jcksnvllxr80/MidiControllerCpp/src/adapters/mcu/WifiManager.cpp

#include "mc/adapters/mcu/WifiManager.h"

#include <algorithm>

#include "mc/adapters/mcu/Log.h"

#include "pico/cyw43_arch.h"
#include "pico/time.h"  // to_ms_since_boot / get_absolute_time

#include "lwip/apps/mdns.h"
#include "lwip/ip4_addr.h"
#include "lwip/netif.h"
#include "lwip/pbuf.h"
#include "lwip/tcp.h"

#include <nlohmann/json.hpp>

#include "mc/app/EditorProtocol.h"

namespace mc::mcu {

namespace {
using json = nlohmann::json;

constexpr uint32_t kConnectTimeoutMs = 15000;  // give up one async join attempt after this
constexpr uint32_t kRetryIntervalMs = 5000;    // wait before re-trying after a failure / drop
uint32_t nowMs() { return to_ms_since_boot(get_absolute_time()); }

err_t tcpRecvTramp(void* arg, tcp_pcb* pcb, pbuf* p, err_t err) {
    auto* self = static_cast<WifiManager*>(arg);
    if (p == nullptr) {
        self->onRecv(pcb, nullptr, 0, true);
        return ERR_OK;
    }
    if (err == ERR_OK) {
        for (pbuf* q = p; q; q = q->next) self->onRecv(pcb, q->payload, q->len, false);
        tcp_recved(pcb, p->tot_len);
    }
    pbuf_free(p);
    return ERR_OK;
}
err_t tcpSentTramp(void* arg, tcp_pcb*, u16_t) {
    static_cast<WifiManager*>(arg)->onSent();
    return ERR_OK;
}
void tcpErrTramp(void* arg, err_t) { static_cast<WifiManager*>(arg)->onClientErr(); }
err_t tcpAcceptTramp(void* arg, tcp_pcb* newpcb, err_t err) {
    if (err != ERR_OK || newpcb == nullptr) return ERR_VAL;
    static_cast<WifiManager*>(arg)->onAccept(newpcb);
    return ERR_OK;
}
void mdnsSrvTxt(struct mdns_service* service, void* /*txt_userdata*/) {
    mdns_resp_add_service_txtitem(service, "version=1", 9);
}
}  // namespace

WifiManager::WifiManager(IConfigStore& store, uint16_t tcpPort) : store_(store), port_(tcpPort) {}

void WifiManager::emitStatus(const std::string& msg) {
    if (statusSink_) statusSink_(msg);
}

void WifiManager::loadConfig() {
    if (!store_.exists("wifi.json")) return;
    try {
        auto j = json::parse(store_.read("wifi.json"));
        ssid_ = j.value("ssid", std::string());
        password_ = j.value("password", std::string());
        enabled_ = j.value("enabled", false);
    } catch (...) {
        // corrupt config -> ignore, stay off
    }
}

void WifiManager::saveConfig() {
    json j;
    j["ssid"] = ssid_;
    j["password"] = password_;
    j["enabled"] = enabled_;
    store_.write("wifi.json", j.dump());
}

void WifiManager::begin() {
    loadConfig();
    LOG_I("wifi", "begin enabled=%d ssid='%s'", (int)enabled_, ssid_.c_str());
    if (cyw43_arch_init()) {
        LOG_E("wifi", "cyw43 init failed");
        emitStatus("WiFi: init failed");
        return;
    }
    inited_ = true;
    cyw43_arch_enable_sta_mode();
    if (enabled_ && !ssid_.empty()) startConnect();  // non-blocking; poll() drives it
}

void WifiManager::poll() {
    if (!inited_) return;
    cyw43_arch_poll();
    serviceLink();
}

// Kick off a non-blocking join. The outcome is observed in serviceLink() via the
// link status, so this returns immediately and never stalls the main loop.
void WifiManager::startConnect() {
    if (!inited_ || !enabled_ || ssid_.empty()) return;
    uint32_t auth = password_.empty() ? CYW43_AUTH_OPEN : CYW43_AUTH_WPA2_AES_PSK;
    lastAttemptMs_ = nowMs();
    LOG_I("wifi", "connecting to '%s'", ssid_.c_str());
    if (cyw43_arch_wifi_connect_async(ssid_.c_str(), password_.c_str(), auth) != 0) {
        link_ = Link::Idle;  // couldn't even start -> serviceLink() retries after backoff
        LOG_E("wifi", "connect async start failed");
        emitStatus("WiFi: connect failed");
        return;
    }
    link_ = Link::Connecting;
    connectStartMs_ = lastAttemptMs_;
    emitStatus("WiFi: connecting");
}

// The point of this rewrite: a non-blocking state machine that finishes the boot
// join without stalling, reconnects automatically if the link drops, and never
// blocks long enough to trip the watchdog.
void WifiManager::serviceLink() {
    if (!enabled_ || ssid_.empty()) return;  // nothing to maintain
    int st = cyw43_tcpip_link_status(&cyw43_state, CYW43_ITF_STA);
    switch (link_) {
        case Link::Connecting:
            if (st == CYW43_LINK_UP) {
                onLinkUp();
            } else if (st < 0 || (nowMs() - connectStartMs_) > kConnectTimeoutMs) {
                connected_ = false;  // failed (bad auth / no net) or timed out
                ip_.clear();
                link_ = Link::Idle;
                lastAttemptMs_ = nowMs();
                LOG_W("wifi", "connect failed/timeout (st=%d) retrying in %lus", st, (unsigned long)(kRetryIntervalMs/1000));
                emitStatus("WiFi: retrying");
            }
            break;
        case Link::Up:
            if (st != CYW43_LINK_UP) {  // dropped under us
                connected_ = false;
                ip_.clear();
                teardownNet();
                link_ = Link::Idle;
                lastAttemptMs_ = nowMs();
                LOG_W("wifi", "link lost (st=%d)", st);
                emitStatus("WiFi: link lost");
            }
            break;
        case Link::Idle:
            if (nowMs() - lastAttemptMs_ >= kRetryIntervalMs) startConnect();
            break;
    }
}

void WifiManager::onLinkUp() {
    link_ = Link::Up;
    connected_ = true;
    ip_ = ip4addr_ntoa(netif_ip4_addr(netif_default));
    startServer();  // rebinds if a previous drop tore it down
    startMdns();
    LOG_I("wifi", "connected ssid='%s' ip=%s port=%u", ssid_.c_str(), ip_.c_str(), port_);
    emitStatus("WiFi " + ip_);
}

void WifiManager::teardownNet() {
    if (client_) {
        tcp_arg(client_, nullptr);
        tcp_close(client_);
        client_ = nullptr;
    }
    if (listen_) {
        tcp_close(listen_);
        listen_ = nullptr;
    }
    rxLine_.clear();
    outbox_.clear();
    outSent_ = 0;
}

void WifiManager::disconnectNow() {
    LOG_I("wifi", "disconnecting");
    teardownNet();
    if (inited_) cyw43_wifi_leave(&cyw43_state, CYW43_ITF_STA);
    link_ = Link::Idle;
    connected_ = false;
    ip_.clear();
    emitStatus("WiFi: off");
}

void WifiManager::startServer() {
    if (listen_) return;
    tcp_pcb* p = tcp_new_ip_type(IPADDR_TYPE_ANY);
    if (!p) return;
    if (tcp_bind(p, IP_ANY_TYPE, port_) != ERR_OK) {
        tcp_close(p);
        return;
    }
    listen_ = tcp_listen_with_backlog(p, 1);
    if (!listen_) {
        tcp_close(p);
        return;
    }
    tcp_arg(listen_, this);
    tcp_accept(listen_, tcpAcceptTramp);
}

void WifiManager::startMdns() {
    if (mdnsUp_) return;
    mdns_resp_init();
    mdns_resp_add_netif(netif_default, "midicontroller");
    mdns_resp_add_service(netif_default, "MidiController", "_midicontroller", DNSSD_PROTO_TCP, port_, mdnsSrvTxt,
                          nullptr);
    mdnsUp_ = true;
}

void WifiManager::onAccept(tcp_pcb* newpcb) {
    LOG_I("wifi", "TCP client connected (replacing=%d)", client_ != nullptr);
    if (client_) {  // single client: replace the old one
        tcp_arg(client_, nullptr);
        tcp_close(client_);
    }
    client_ = newpcb;
    rxLine_.clear();
    outbox_.clear();
    outSent_ = 0;
    tcp_arg(client_, this);
    tcp_recv(client_, tcpRecvTramp);
    tcp_sent(client_, tcpSentTramp);
    tcp_err(client_, tcpErrTramp);
}

void WifiManager::onRecv(tcp_pcb* pcb, const void* data, uint16_t len, bool closed) {
    if (closed) {
        if (client_ == pcb) {
            LOG_I("wifi", "TCP client disconnected");
            tcp_arg(pcb, nullptr);
            tcp_close(pcb);
            client_ = nullptr;
            rxLine_.clear();
            outbox_.clear();
            outSent_ = 0;
        }
        return;
    }
    const char* p = static_cast<const char*>(data);
    for (uint16_t i = 0; i < len; ++i) {
        char c = p[i];
        if (c == '\n') {
            LOG_D("wifi", "cmd (%zu): %.120s%s", rxLine_.size(), rxLine_.c_str(),
                  rxLine_.size() > 120 ? "..." : "");
            if (proto_) outbox_ += proto_->handleLine(rxLine_);
            rxLine_.clear();
        } else if (c != '\r' && rxLine_.size() < 128 * 1024) {
            rxLine_.push_back(c);
        }
    }
    trySend();
}

void WifiManager::trySend() {
    if (!client_) return;
    while (outSent_ < outbox_.size()) {
        u16_t avail = tcp_sndbuf(client_);
        if (avail == 0) break;
        u16_t n = static_cast<u16_t>(std::min<size_t>(avail, outbox_.size() - outSent_));
        if (tcp_write(client_, outbox_.data() + outSent_, n, TCP_WRITE_FLAG_COPY) != ERR_OK) break;
        outSent_ += n;
    }
    tcp_output(client_);
    if (outSent_ >= outbox_.size()) {
        outbox_.clear();
        outSent_ = 0;
    }
}

void WifiManager::onSent() { trySend(); }

void WifiManager::onClientErr() {
    LOG_W("wifi", "TCP client error — connection dropped");
    client_ = nullptr;  // lwIP already freed the pcb
    rxLine_.clear();
    outbox_.clear();
    outSent_ = 0;
}

void WifiManager::setCredentials(const std::string& ssid, const std::string& password) {
    ssid_ = ssid;
    password_ = password;
    enabled_ = true;  // setting credentials implies "use this network"
    saveConfig();
    if (inited_) {
        disconnectNow();  // leave any old network + tear down
        startConnect();   // non-blocking join to the new one
    }
}

void WifiManager::setEnabled(bool on) {
    enabled_ = on;
    saveConfig();
    if (!inited_) return;
    if (on) {
        if (link_ == Link::Idle) startConnect();  // no-op if already connecting/up
    } else {
        disconnectNow();
    }
}

WifiStatus WifiManager::status() const {
    WifiStatus s;
    s.enabled = enabled_;
    s.connected = connected_;
    s.ssid = ssid_;
    s.ip = ip_;
    return s;
}

}  // namespace mc::mcu
