jcksnvllxr80/MidiControllerCpp/include/mc/app/Application.h

#pragma once
//
// Application — the composition root and event loop. Ports the setup()/main()
// glue from midi_controller.py plus the song/set/part navigation from
// RotaryEncoder.py:
//   * builds MidiPedals from the channel table (in channel order)
//   * footswitches preview (displayed) song/part; "Select" commits (loads MIDI)
//   * long-press footswitches commit immediately (change_and_select)
//   * the rotary knob drives the MenuTree (setup/global/power)
//
// All hardware is behind ports, so the same Application runs on the sim now and
// the microcontroller later.
//
#include <algorithm>
#include <functional>
#include <map>
#include <memory>
#include <string>
#include <vector>

#include "mc/domain/ControllerState.h"
#include "mc/domain/MenuTree.h"
#include "mc/domain/MidiPedal.h"
#include "mc/domain/PedalConfig.h"
#include "mc/domain/SongPartSet.h"
#include "mc/ports/IClock.h"
#include "mc/ports/IConfigStore.h"
#include "mc/ports/IConfigTransport.h"
#include "mc/ports/IDisplay.h"
#include "mc/ports/IInput.h"
#include "mc/ports/ILed.h"
#include "mc/ports/IMidiOut.h"

namespace mc {

class Application {
public:
    struct Ports {
        IConfigStore* store = nullptr;
        IMidiOut* midi = nullptr;
        IDisplay* display = nullptr;
        ILed* led = nullptr;
        IClock* clock = nullptr;
        IInput* input = nullptr;
        IConfigTransport* transport = nullptr;  // optional
    };

    explicit Application(Ports ports);

    void setup();        // load config, build pedals/menu, set initial display
    void run();          // poll input -> dispatch until Quit / source exhausted
    bool handleEvent(const InputEvent& ev);  // false => stop loop
    void tick();         // periodic housekeeping (debounced "save defaults"); call each loop iter

    // Optional: invoked once per handled input/command (physical or editor) so a
    // host can flash an activity indicator. Portable code stays hardware-agnostic.
    void setActivitySink(std::function<void()> fn) { activitySink_ = std::move(fn); }

    bool setupFailed() const { return setupFailed_; }  // config parse fell back to a safe shell

    // --- inspectors (for tests) ---
    ControllerState& state() { return state_; }
    Setlist& setlist() { return setlist_; }
    MenuTree& menu() { return menu_; }
    const std::string& currentSongName() const { return currentSong().name; }
    const std::string& currentPartName() const { return currentPart().name; }
    const std::string& displayedSongName() const { return displayedSong().name; }
    const std::string& displayedPartName() const { return displayedPart().name; }
    const std::string& displayedMessage() const { return lastMessage_; }  // last text shown
    bool quitRequested() const { return quitRequested_; }

    // Navigation, exposed so tests/menus can drive them directly.
    void loadPart();
    void loadSong();
    void selectChoice();
    void nextSong();
    void prevSong();
    void nextPart();
    void prevPart();

private:
    // Bounds-safe so a corrupt/empty config (see setup()'s fallback) degrades to a
    // blank song/part instead of throwing out_of_range and taking the device down.
    const Song& songAt(int i) const {
        static const Song kEmpty;
        if (setlist_.songs.empty()) return kEmpty;
        return setlist_.songs[std::min(std::max(i, 0), static_cast<int>(setlist_.songs.size()) - 1)];
    }
    static const Part& partAt(const Song& s, int i) {
        static const Part kEmpty;
        if (s.parts.empty()) return kEmpty;
        return s.parts[std::min(std::max(i, 0), static_cast<int>(s.parts.size()) - 1)];
    }
    const Song& currentSong() const { return songAt(currentSongIdx_); }
    const Part& currentPart() const { return partAt(currentSong(), currentPartIdx_); }
    const Song& displayedSong() const { return songAt(displayedSongIdx_); }
    const Part& displayedPart() const { return partAt(displayedSong(), displayedPartIdx_); }

    void loadSetlist(const std::string& setName);
    void buttonExecutor(const std::string& fn);
    void changeAndSelect(const std::string& fn);
    void setSongInfoMessage();
    void previewMessage();
    void show(const std::string& msg);  // route all display text through here
    std::string songInfoString(const Song& s, const Part& p) const;
    void buildMenu();
    void buildPedalMenu();     // Setup -> Midi Pedals -> pedal -> group -> param (live edit)
    // Lazy builders for the pedal editor — run on first node entry, never at boot.
    void buildPedalGroups(MenuNode* pedalNode, const PedalConfig* cfg, MidiPedal* mp);
    void buildParamLeaves(MenuNode* groupNode, const Action* groupAction, MidiPedal* mp);
    void markDefaultsDirty();  // a commit changed current set/song/part
    void persistDefaults();    // write current set/song/part back to midi_controller.json

    Ports p_;
    ControllerState state_;
    Setlist setlist_;
    std::map<std::string, PedalConfig> pedalConfigs_;
    std::vector<std::unique_ptr<MidiPedal>> pedals_;  // channel order

    int currentSongIdx_ = 0;
    int currentPartIdx_ = 0;
    int displayedSongIdx_ = 0;
    int displayedPartIdx_ = 0;
    bool quitRequested_ = false;
    std::string lastMessage_;
    std::function<void()> activitySink_;  // optional activity-indicator pulse
    bool setupFailed_ = false;       // config parse threw -> running in a safe shell
    bool defaultsDirty_ = false;     // current set/song/part changed, not yet persisted
    double defaultsDirtyAt_ = 0.0;   // clock time of the change (for debounced flush)

    MenuTree menu_{"MidiController"};
    MenuNode* setupMenu_ = nullptr;
    MenuNode* globalMenu_ = nullptr;
    MenuNode* powerMenu_ = nullptr;
    MenuNode* midiPedalsMenu_ = nullptr;  // Setup -> Midi Pedals (per-pedal live editor)
    MenuNode* setsNode_ = nullptr;
    MenuNode* songsNode_ = nullptr;
    MenuNode* partsNode_ = nullptr;
    MenuNode* colorNode_ = nullptr;
    MenuNode* brightnessNode_ = nullptr;
    MenuNode* lockNode_ = nullptr;
};

}  // namespace mc
